Theaninova/Brick-Monorail/STEPs/solid/R28/S8.step

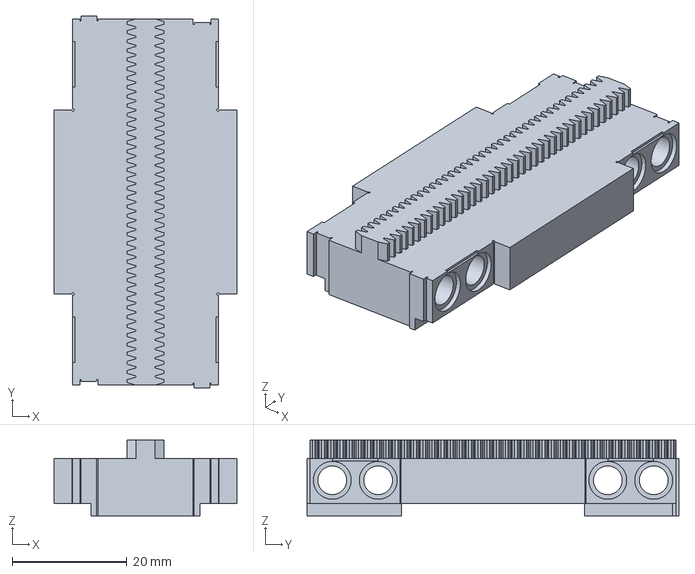
[picture p15: CAD file, 2025-01-19]
STEPs/solid/R28/S8.step
31.8 x 64.8 x 13.2 mm
