Theaninova/Brick-Monorail/STEPs/solid/S5.step

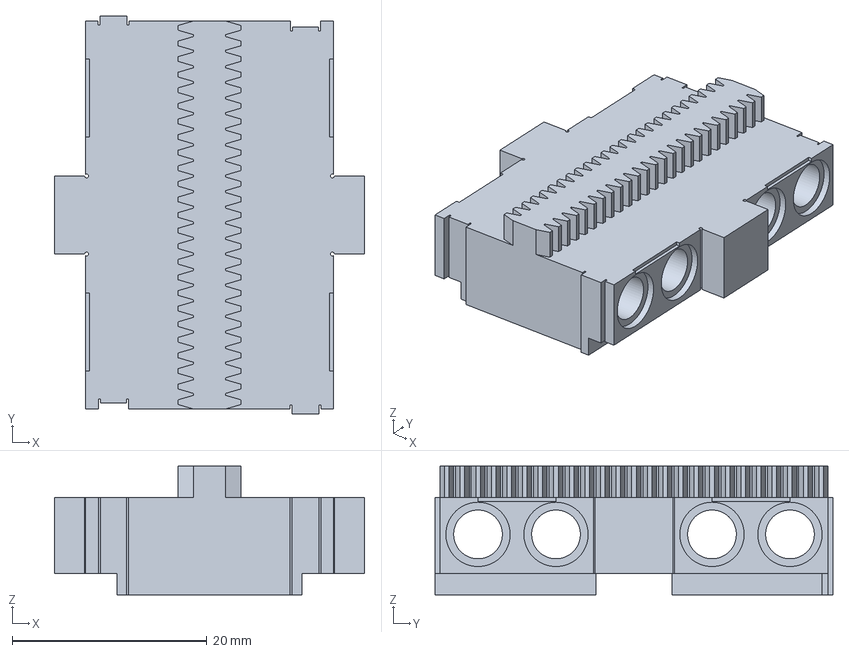
[picture p16: CAD file, 2025-01-19]
STEPs/solid/S5.step
31.8 x 40.8 x 13.2 mm
