Theaninova/Brick-Monorail/STEPs/solid_support/R28/C45_support.step

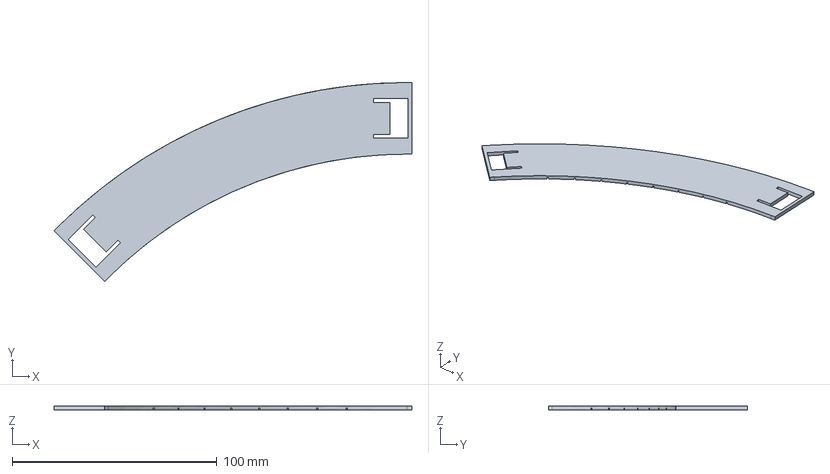
[picture p17: CAD file, 2025-01-19]
STEPs/solid_support/R28/C45_support.step
175.0 x 97.3 x 2.10 mm
