Theaninova/Brick-Monorail/STEPs/solid_support/S5.step

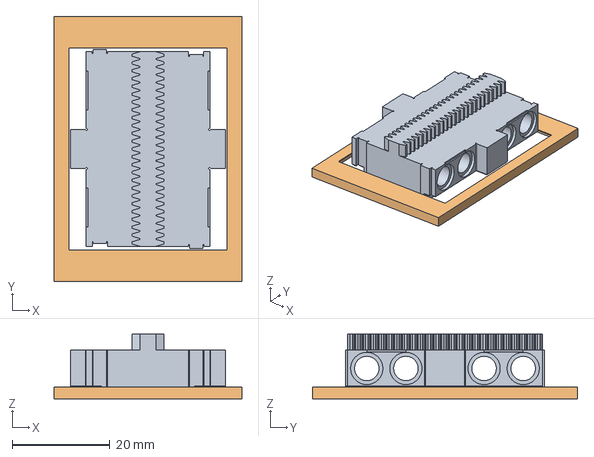
[picture p18: CAD file, 2025-01-19]
STEPs/solid_support/S5.step
38.4 x 54.2 x 13.2 mm
