Theaninova/Brick-Monorail/STEPs/stanchions/2x2x3.step

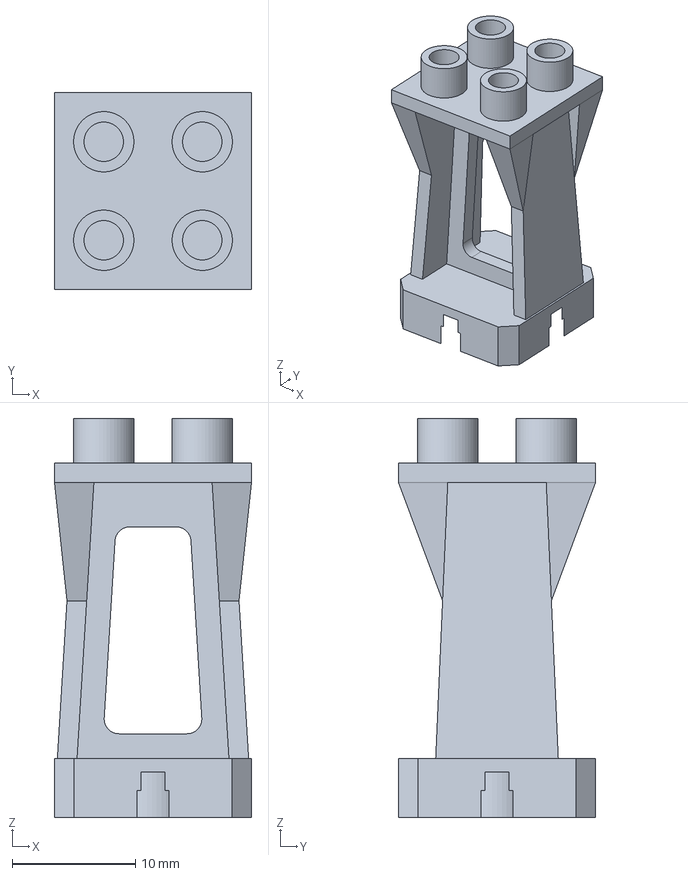
[picture p19: CAD file, 2025-01-19]
STEPs/stanchions/2x2x3.step
16.0 x 16.0 x 32.4 mm
