Theaninova/Brick-Monorail/STEPs/transrapid/S10.step

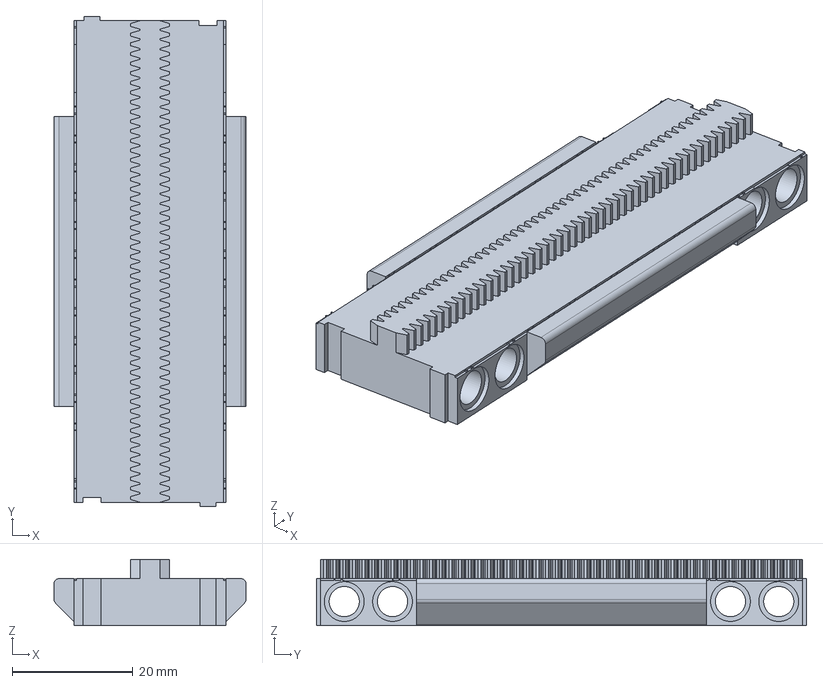
[picture p20: CAD file, 2025-01-19]
STEPs/transrapid/S10.step
31.8 x 81.2 x 11.0 mm
