Theaninova/Brick-Monorail/STEPs/classic/S4.step

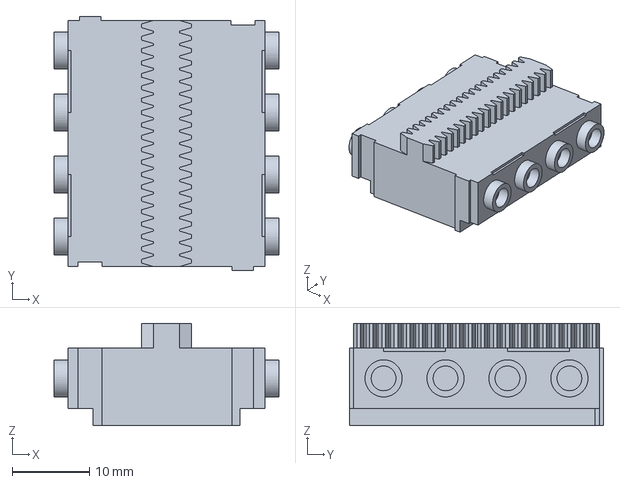
[picture p21: CAD file, 2025-01-19]
STEPs/classic/S4.step
29.0 x 32.8 x 13.2 mm
