Theaninova/Brick-Monorail/STEPs/classic_pop/R28/S8_body.step

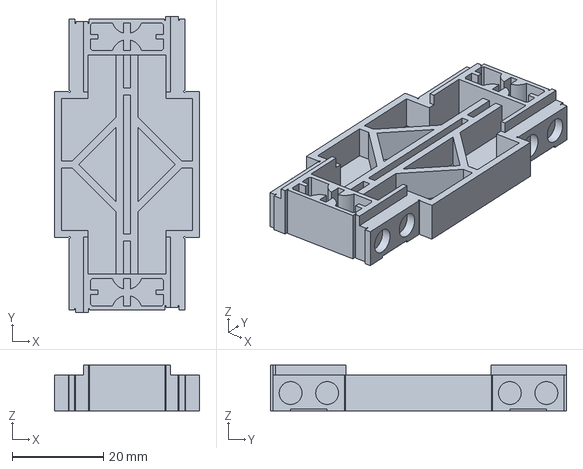
[picture p22: CAD file, 2025-01-19]
STEPs/classic_pop/R28/S8_body.step
31.8 x 64.8 x 10.0 mm
