Theaninova/Brick-Monorail/STEPs/classic_pop/S10_rack.step

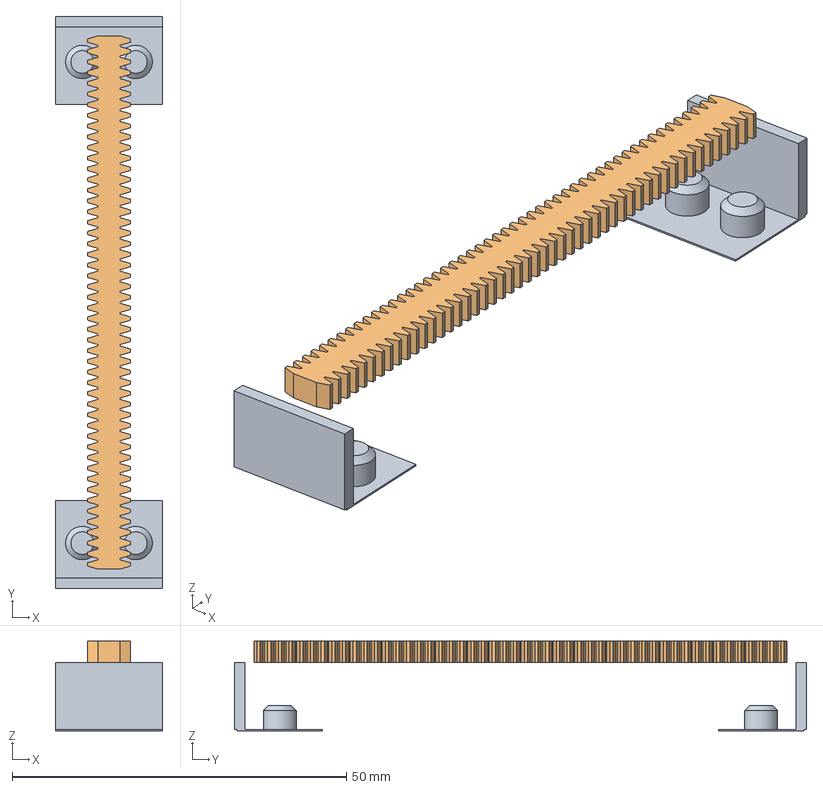
[picture p23: CAD file, 2025-01-19]
STEPs/classic_pop/S10_rack.step
16.0 x 85.6 x 13.4 mm
