Theaninova/Brick-Monorail/STEPs/solid/S15.step

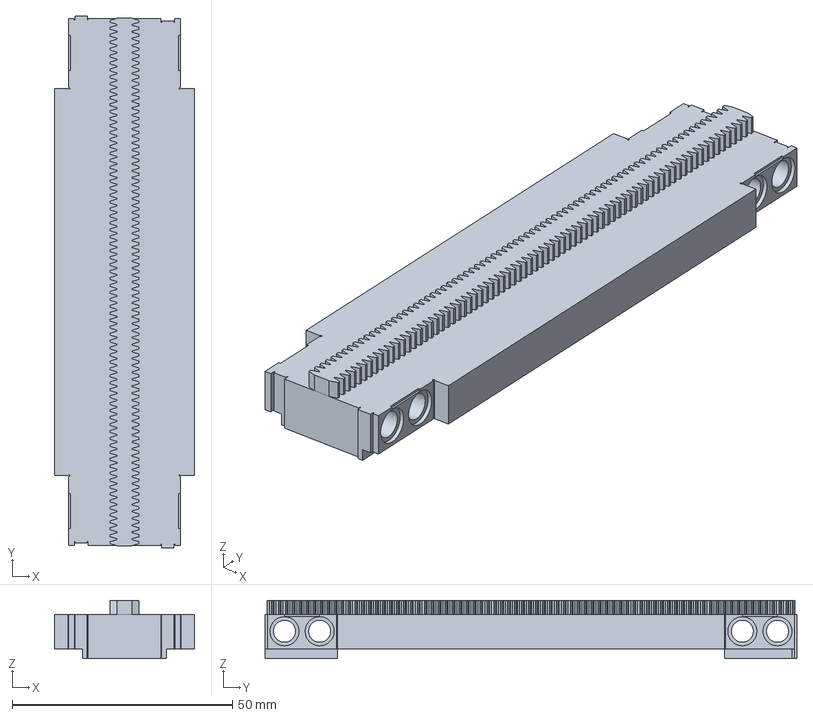
[picture p24: CAD file, 2025-01-19]
STEPs/solid/S15.step
31.8 x 120.8 x 13.2 mm
