Theaninova/Brick-Monorail/STEPs/solid_support/R28/S32_support.step

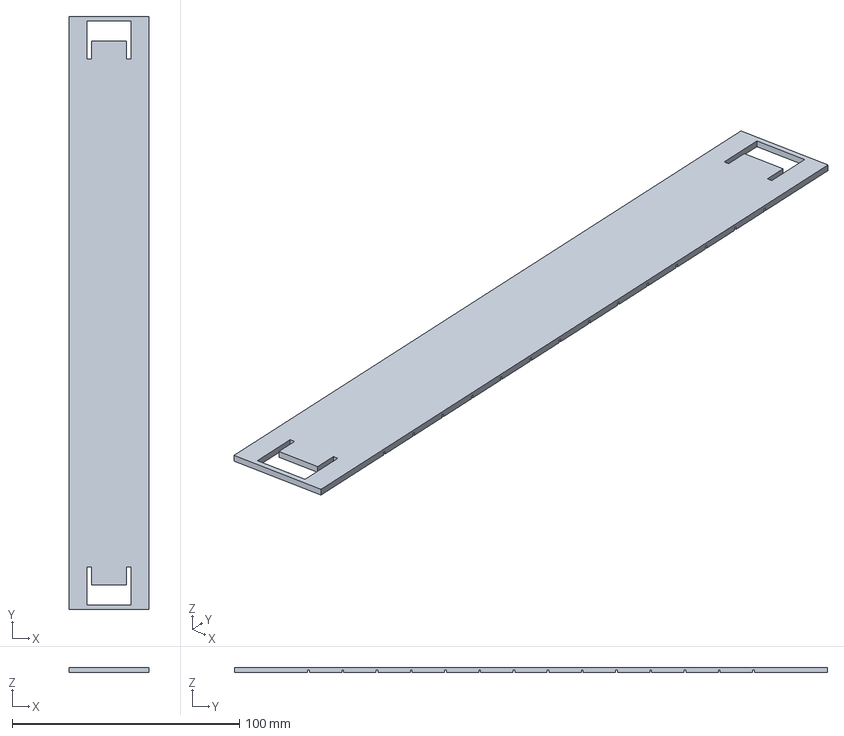
[picture p25: CAD file, 2025-01-19]
STEPs/solid_support/R28/S32_support.step
35.0 x 261.0 x 2.10 mm
