Theaninova/Brick-Monorail/STEPs/solid_support/S5_support.step

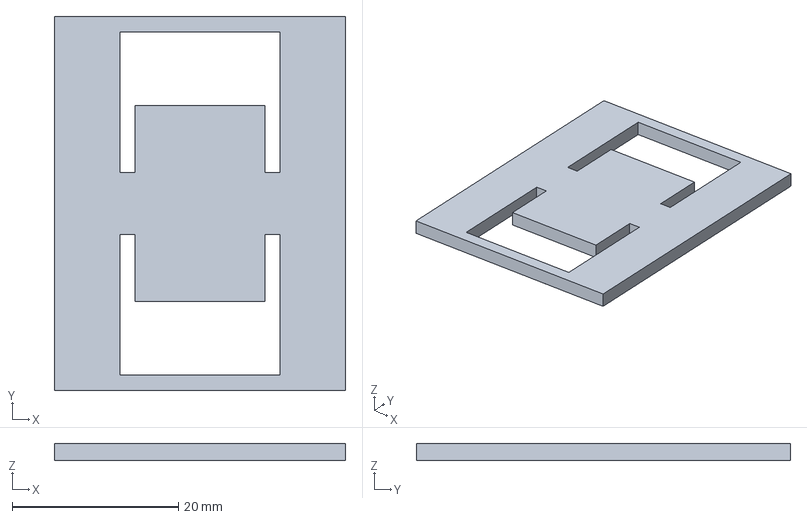
[picture p26: CAD file, 2025-01-19]
STEPs/solid_support/S5_support.step
35.0 x 45.0 x 2.10 mm
