Theaninova/Brick-Monorail/STEPs/stanchions/4x4x4.step

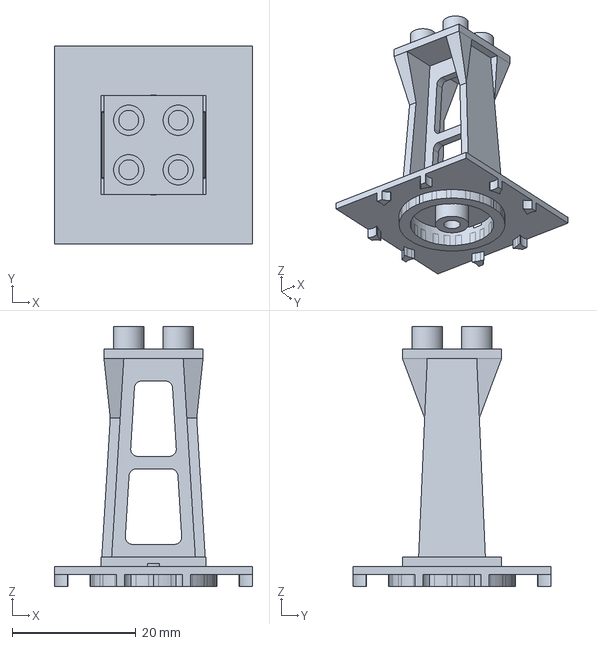
[picture p27: CAD file, 2025-01-19]
STEPs/stanchions/4x4x4.step
32.0 x 32.0 x 42.0 mm
