Theaninova/Brick-Monorail/STEPs/transrapid/C7.step

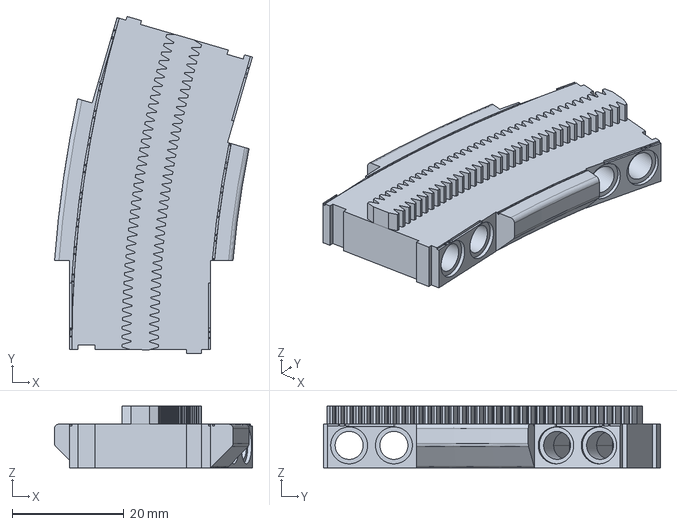
[picture p28: CAD file, 2025-01-19]
STEPs/transrapid/C7.step
35.4 x 60.2 x 11.0 mm
