Theaninova/Brick-Monorail/STEPs/classic/C7.step

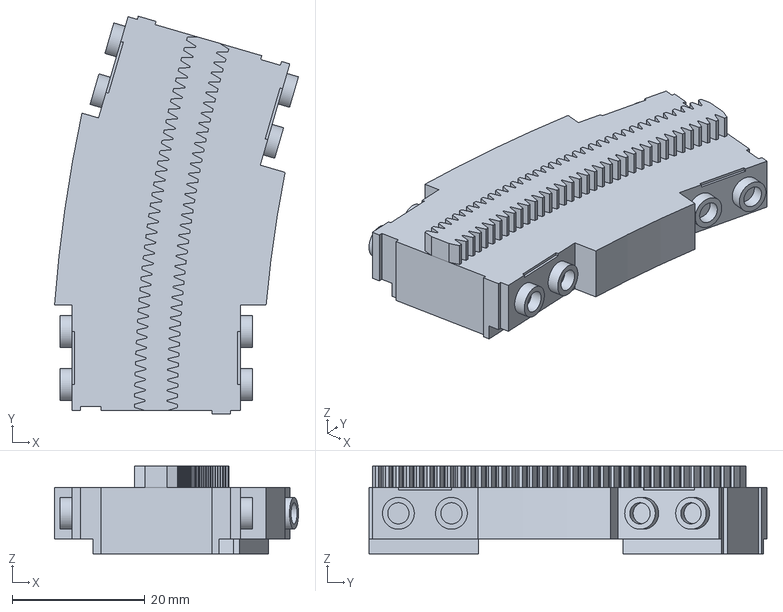
[picture p29: CAD file, 2025-01-19]
STEPs/classic/C7.step
36.8 x 59.9 x 13.2 mm
