Theaninova/Brick-Monorail/STEPs/classic_pop/R28/C45_body.step

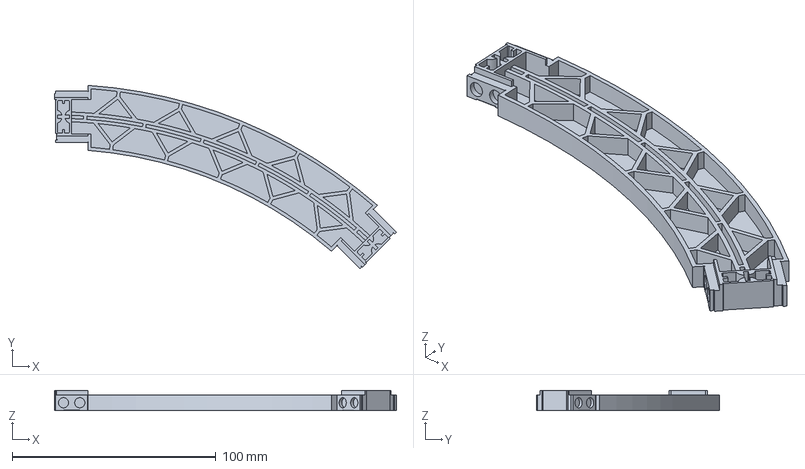
[picture p30: CAD file, 2025-01-19]
STEPs/classic_pop/R28/C45_body.step
167.7 x 89.9 x 10.0 mm
