Theaninova/Brick-Monorail/STEPs/classic_pop/S15_body.step

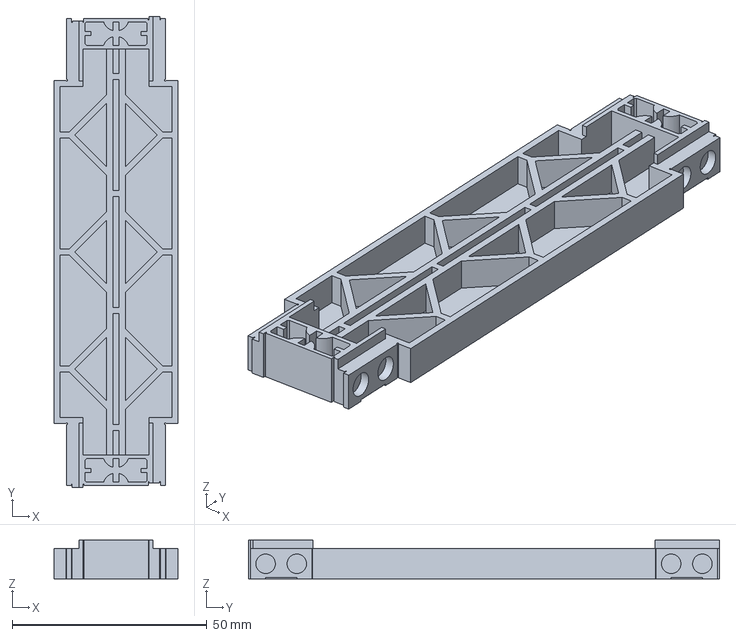
[picture p31: CAD file, 2025-01-19]
STEPs/classic_pop/S15_body.step
31.8 x 120.8 x 10.0 mm
