Theaninova/Brick-Monorail/STEPs/solid/C15.step

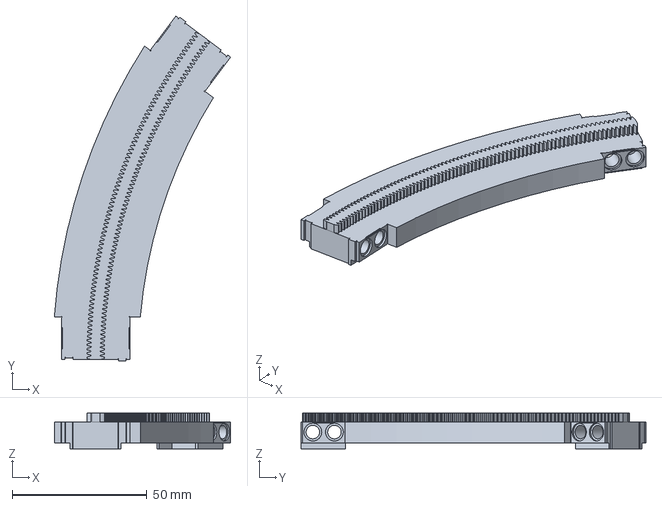
[picture p32: CAD file, 2025-01-19]
STEPs/solid/C15.step
65.4 x 127.9 x 13.2 mm
