Theaninova/Brick-Monorail/STEPs/solid_support/R28/C90_support.step

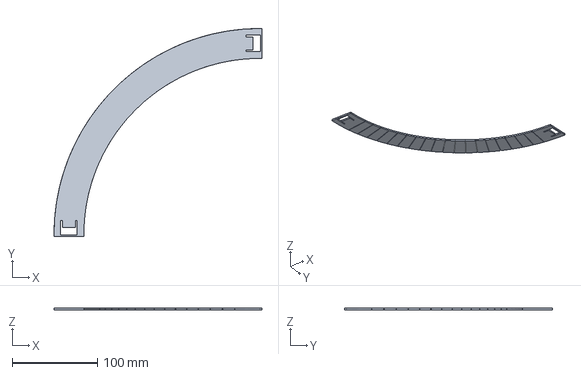
[picture p33: CAD file, 2025-01-19]
STEPs/solid_support/R28/C90_support.step
244.0 x 244.0 x 2.10 mm
