Theaninova/Brick-Monorail/STEPs/solid_support/S4.step

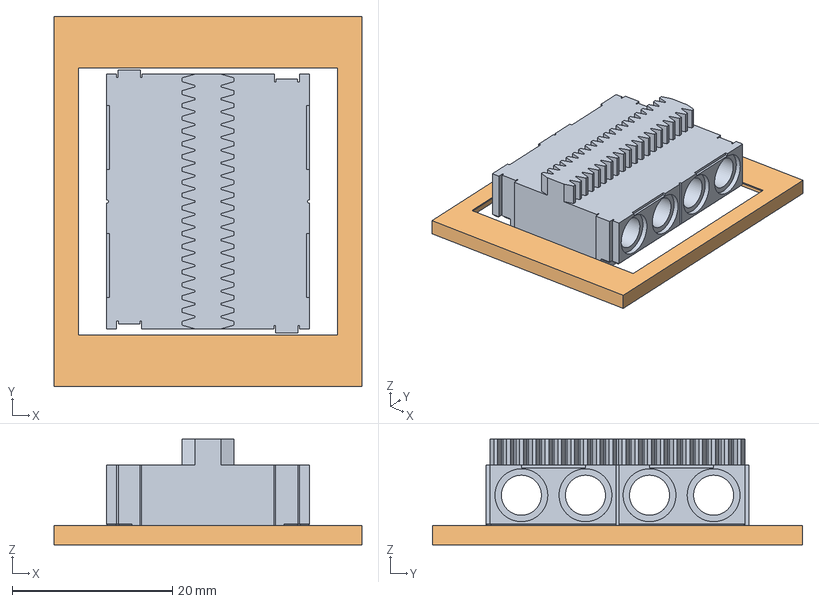
[picture p34: CAD file, 2025-01-19]
STEPs/solid_support/S4.step
38.4 x 46.2 x 13.2 mm
