Theaninova/Brick-Monorail/STEPs/stanchions/4x4x5.step

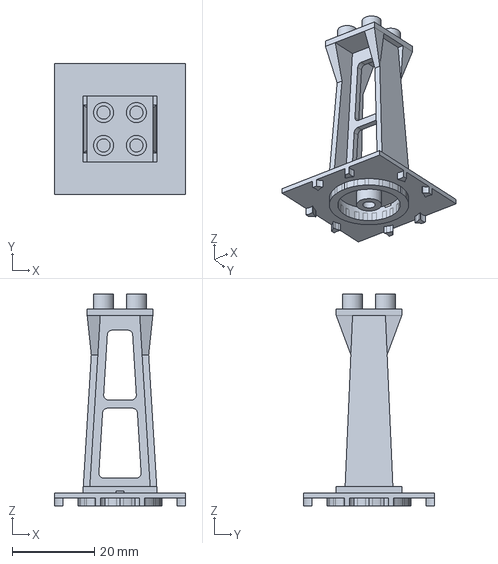
[picture p35: CAD file, 2025-01-19]
STEPs/stanchions/4x4x5.step
32.0 x 32.0 x 51.6 mm
