Theaninova/Brick-Monorail/STEPs/transrapid/S5.step

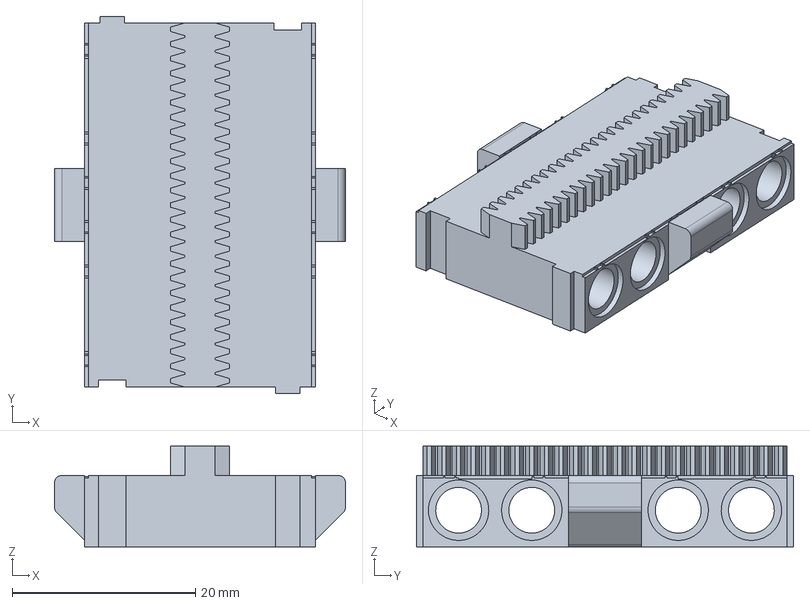
[picture p36: CAD file, 2025-01-19]
STEPs/transrapid/S5.step
31.8 x 41.2 x 11.0 mm
