Theaninova/Brick-Monorail/STEPs/classic/S10.step

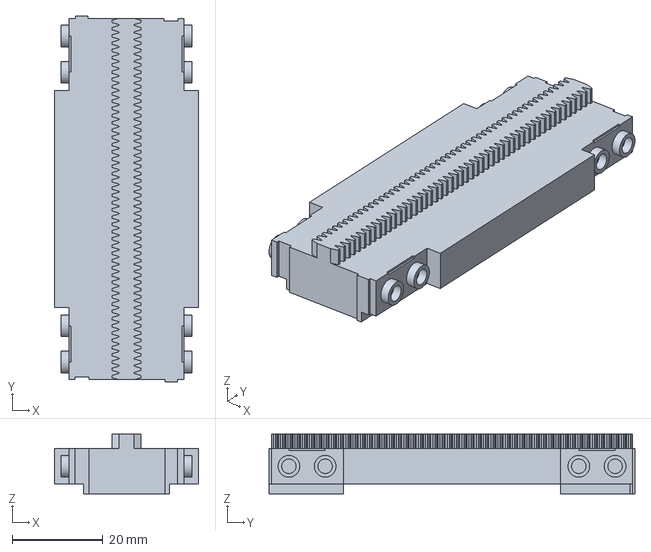
[picture p37: CAD file, 2025-01-19]
STEPs/classic/S10.step
31.8 x 80.8 x 13.2 mm
