Theaninova/Brick-Monorail/STEPs/classic_pop/R28/S8_rack.step

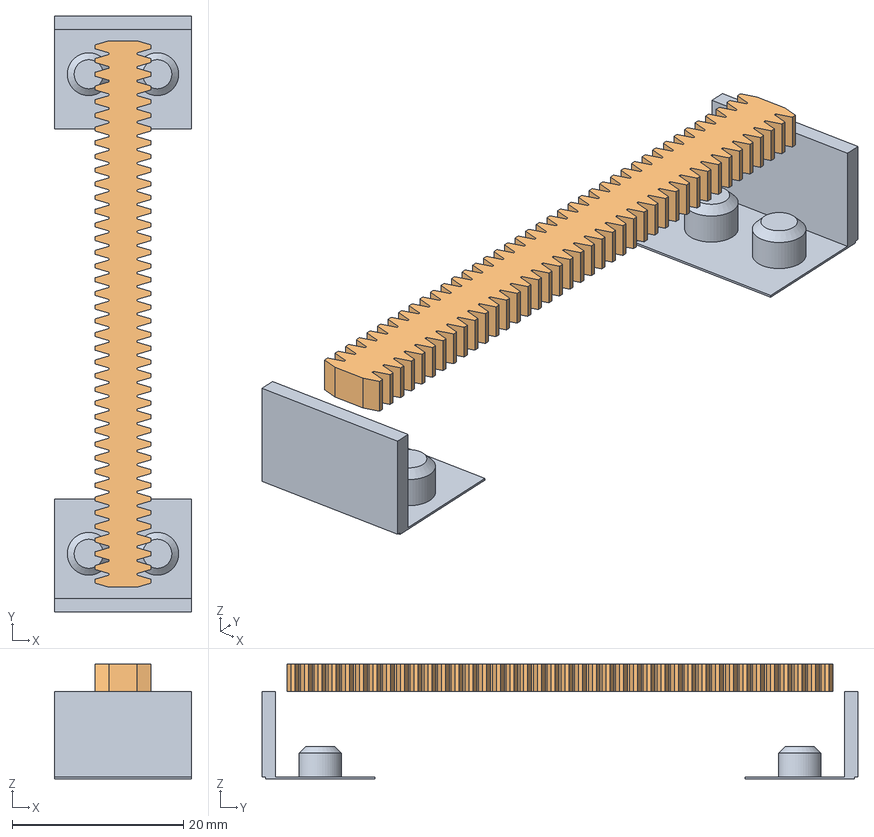
[picture p38: CAD file, 2025-01-19]
STEPs/classic_pop/R28/S8_rack.step
16.0 x 69.6 x 13.4 mm
