Theaninova/Brick-Monorail/STEPs/classic_pop/S25_body.step

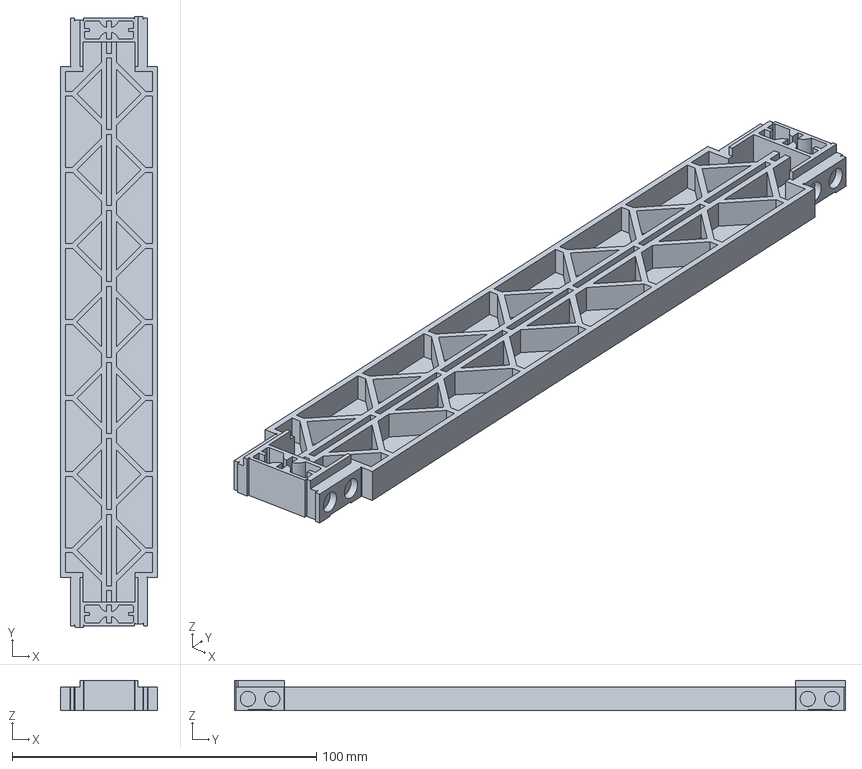
[picture p39: CAD file, 2025-01-19]
STEPs/classic_pop/S25_body.step
31.8 x 200.8 x 10.0 mm
