Theaninova/Brick-Monorail/STEPs/solid/S10.step

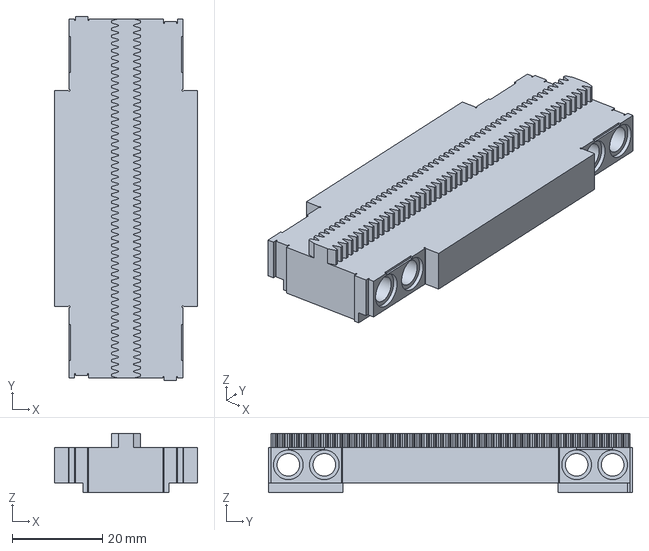
[picture p40: CAD file, 2025-01-19]
STEPs/solid/S10.step
31.8 x 80.8 x 13.2 mm
