Theaninova/Brick-Monorail/STEPs/solid_support/R28/S16_support.step

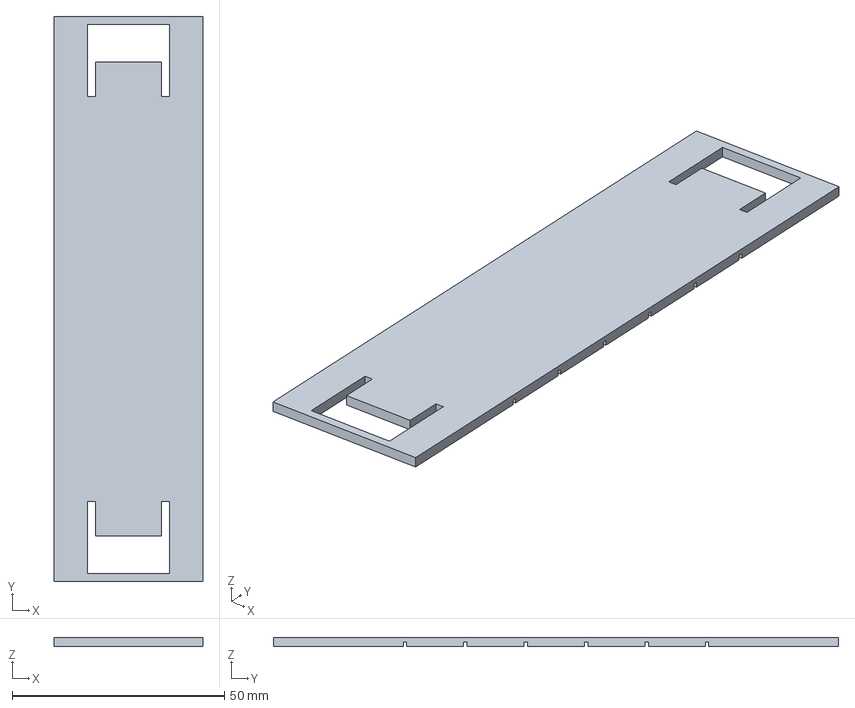
[picture p41: CAD file, 2025-01-19]
STEPs/solid_support/R28/S16_support.step
35.0 x 133.0 x 2.10 mm
