Theaninova/Brick-Monorail/STEPs/solid_support/S10_support.step

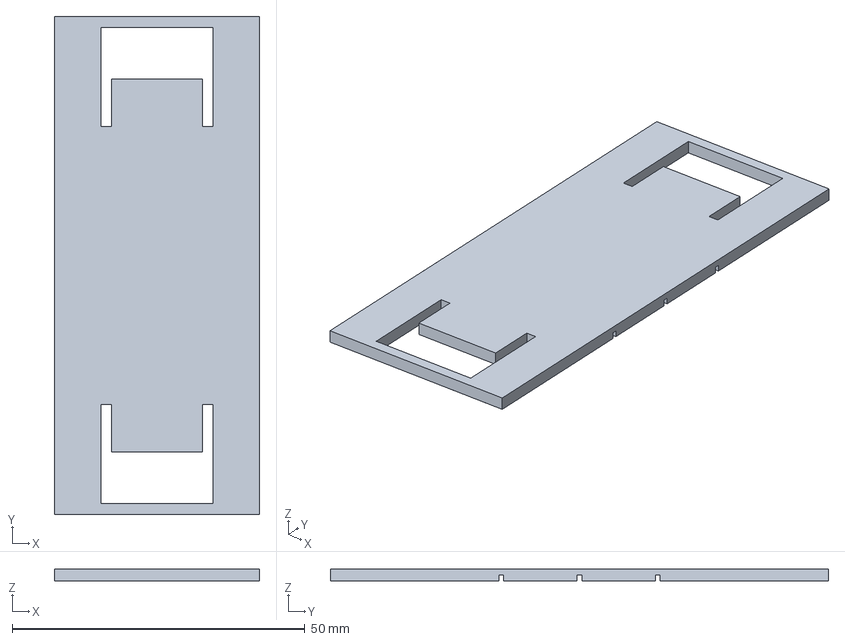
[picture p42: CAD file, 2025-01-19]
STEPs/solid_support/S10_support.step
35.0 x 85.0 x 2.10 mm
