Theaninova/Brick-Monorail/STEPs/stanchions/4x4x3.step

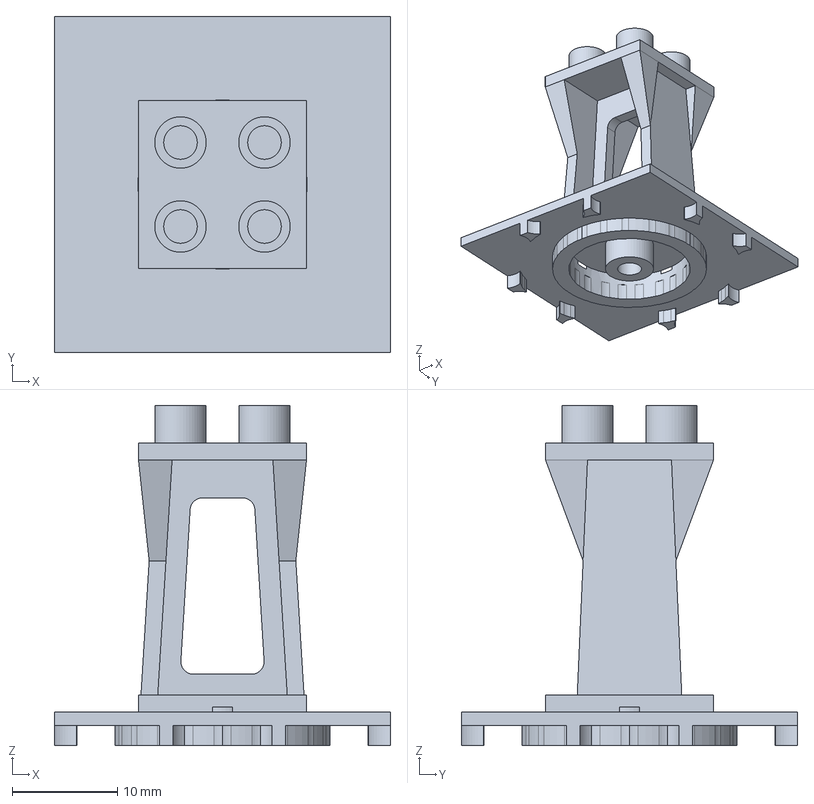
[picture p43: CAD file, 2025-01-19]
STEPs/stanchions/4x4x3.step
32.0 x 32.0 x 32.4 mm
