Theaninova/Brick-Monorail/STEPs/classic_pop/R28/C90_body.step

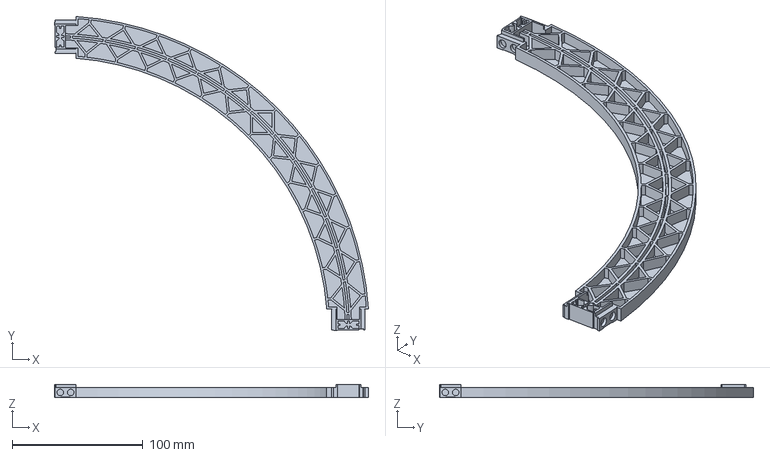
[picture p44: CAD file, 2025-01-19]
STEPs/classic_pop/R28/C90_body.step
239.8 x 239.8 x 10.0 mm
