Theaninova/Brick-Monorail/STEPs/classic_pop/S5_rack.step

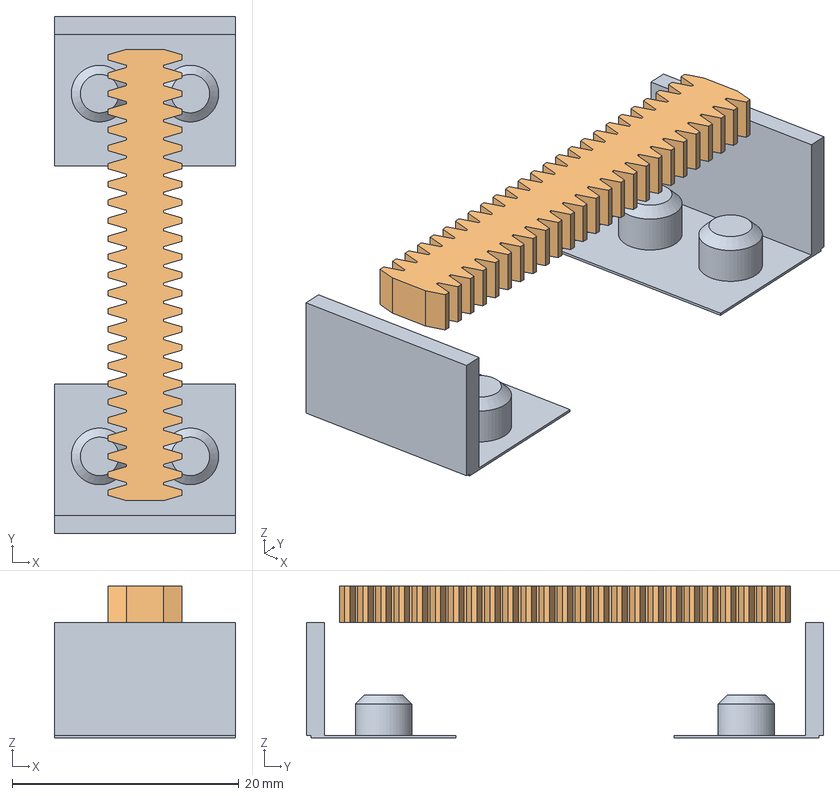
[picture p45: CAD file, 2025-01-19]
STEPs/classic_pop/S5_rack.step
16.0 x 45.6 x 13.4 mm
