Theaninova/Brick-Monorail/STEPs/solid/C7.step

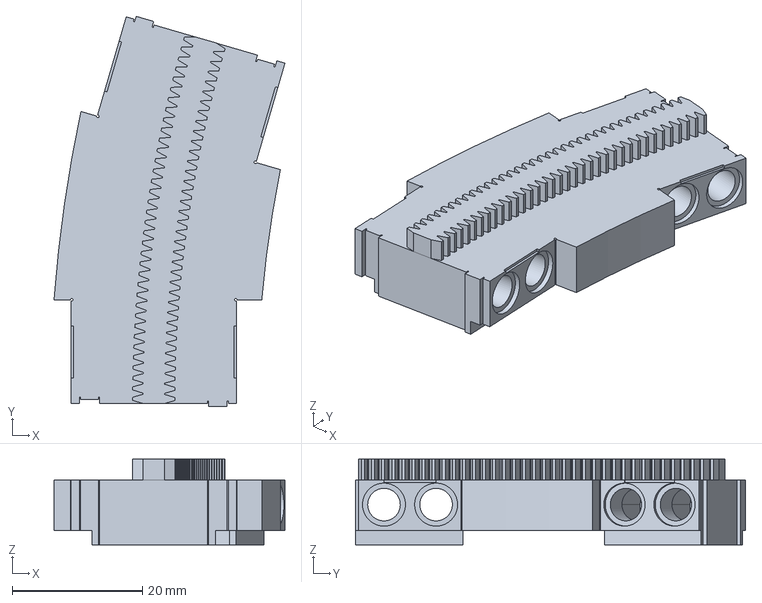
[picture p46: CAD file, 2025-01-19]
STEPs/solid/C7.step
35.5 x 59.9 x 13.2 mm
