Theaninova/Brick-Monorail/STEPs/solid_support/R28/S8_support.step

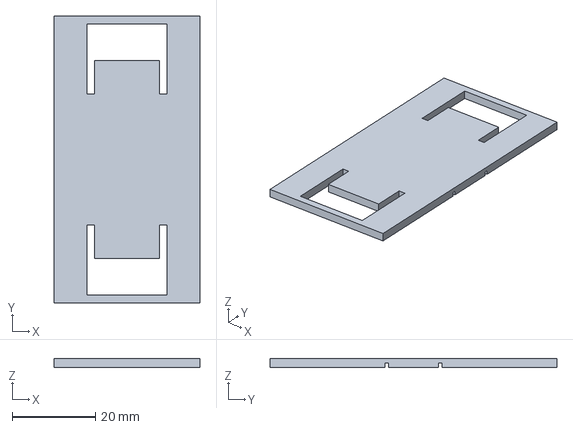
[picture p47: CAD file, 2025-01-19]
STEPs/solid_support/R28/S8_support.step
35.0 x 69.0 x 2.10 mm
