Theaninova/Brick-Monorail/STEPs/solid_support/S10.step

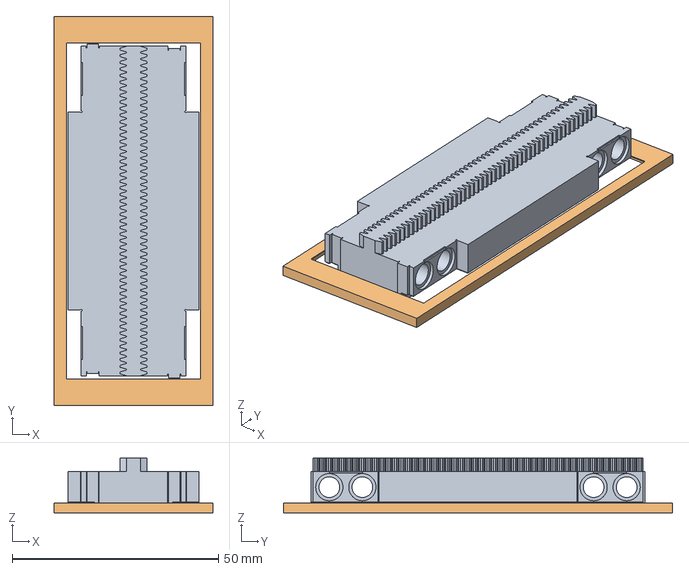
[picture p48: CAD file, 2025-01-19]
STEPs/solid_support/S10.step
38.4 x 94.2 x 13.2 mm
