Theaninova/Brick-Monorail/STEPs/stanchions/2x2x1.step

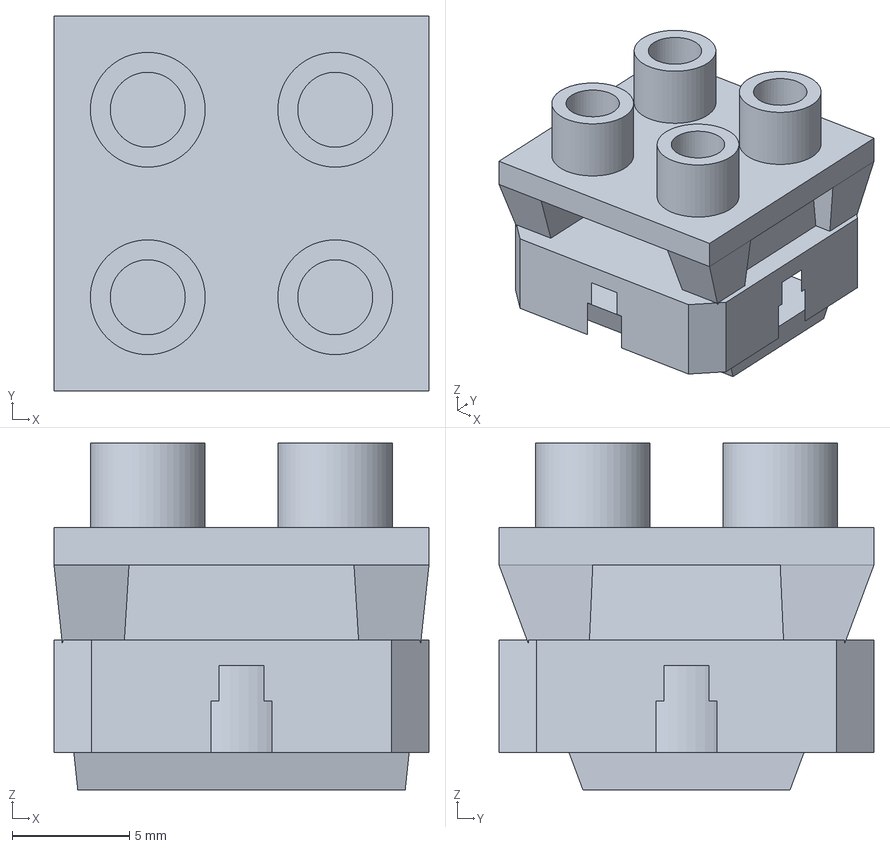
[picture p49: CAD file, 2025-01-19]
STEPs/stanchions/2x2x1.step
16.0 x 16.0 x 14.8 mm
