Theaninova/Brick-Monorail/STEPs/classic_pop/C15_body.step

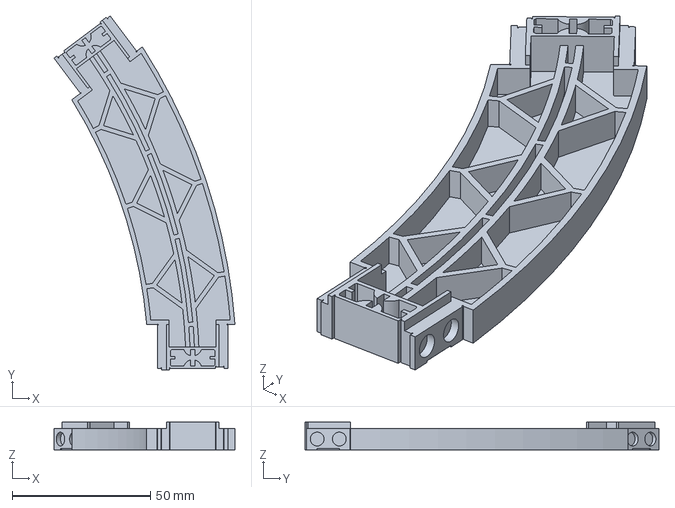
[picture p50: CAD file, 2025-01-19]
STEPs/classic_pop/C15_body.step
65.4 x 127.9 x 10.0 mm
