Theaninova/Brick-Monorail/STEPs/classic_pop/R28/S32_body.step

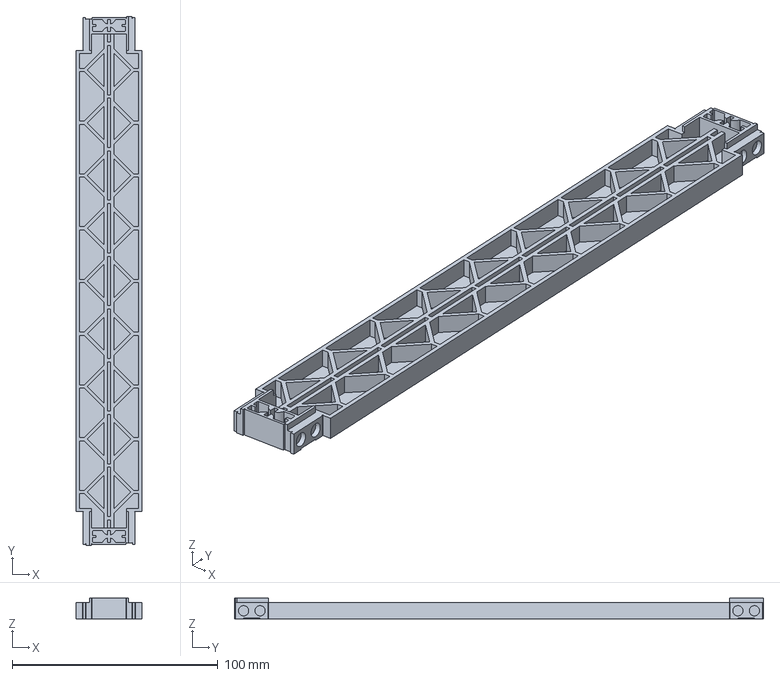
[picture p51: CAD file, 2025-01-19]
STEPs/classic_pop/R28/S32_body.step
31.8 x 256.8 x 10.0 mm
