Theaninova/Brick-Monorail/STEPs/solid_support/R28/S16.step

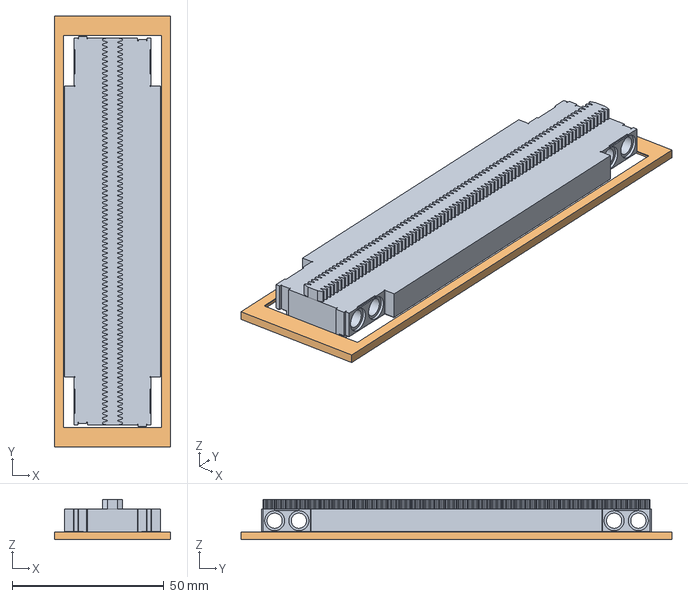
[picture p52: CAD file, 2025-01-19]
STEPs/solid_support/R28/S16.step
38.4 x 142.2 x 13.2 mm
