Theaninova/Brick-Monorail/STEPs/solid_support/S15.step

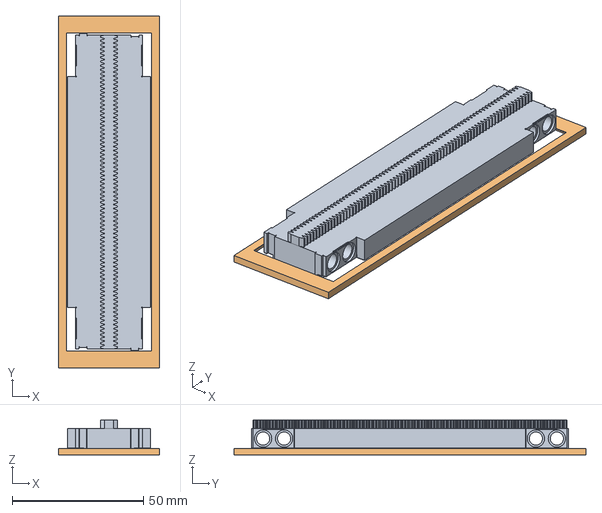
[picture p53: CAD file, 2025-01-19]
STEPs/solid_support/S15.step
38.4 x 134.2 x 13.2 mm
