Theaninova/Brick-Monorail/STEPs/stanchions/6x6x10.step

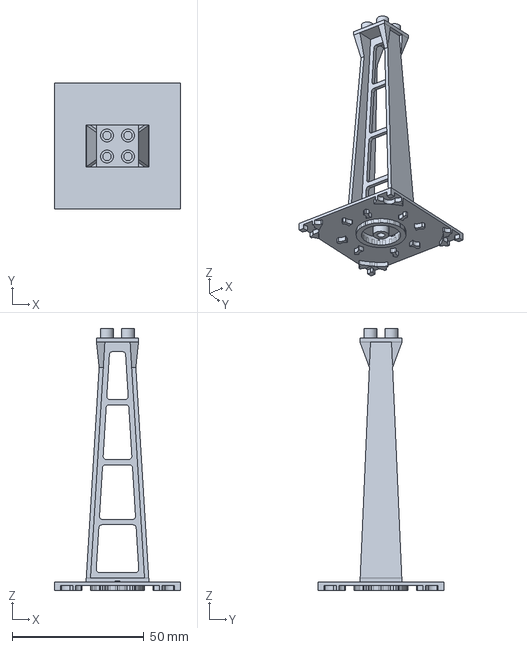
[picture p54: CAD file, 2025-01-19]
STEPs/stanchions/6x6x10.step
48.0 x 48.0 x 99.6 mm
