Theaninova/Brick-Monorail/STEPs/classic_pop/S10_body.step

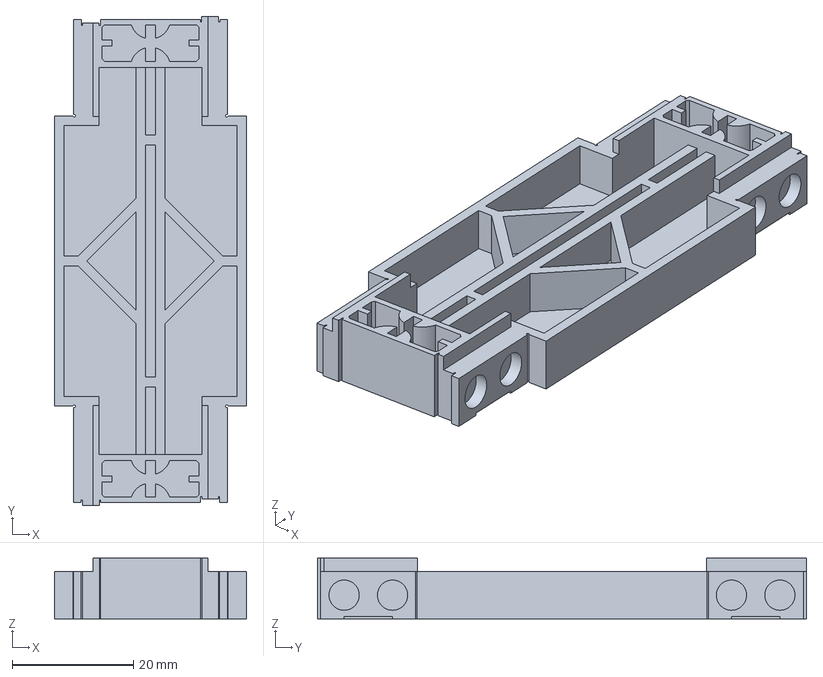
[picture p55: CAD file, 2025-01-19]
STEPs/classic_pop/S10_body.step
31.8 x 80.8 x 10.0 mm
