Theaninova/Brick-Monorail/STEPs/solid_support/C7.step

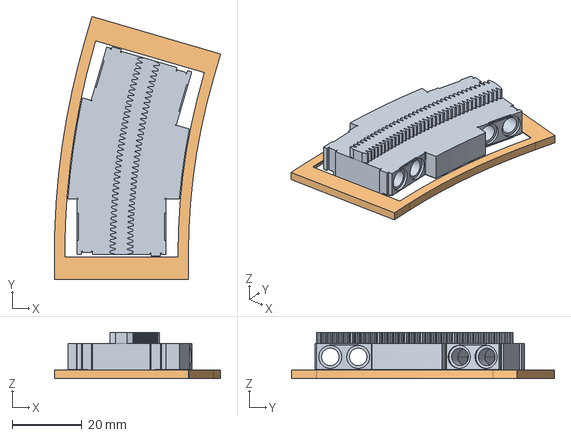
[picture p56: CAD file, 2025-01-19]
STEPs/solid_support/C7.step
47.6 x 75.3 x 13.2 mm
