Theaninova/Brick-Monorail/STEPs/stanchions/2x2x2.step

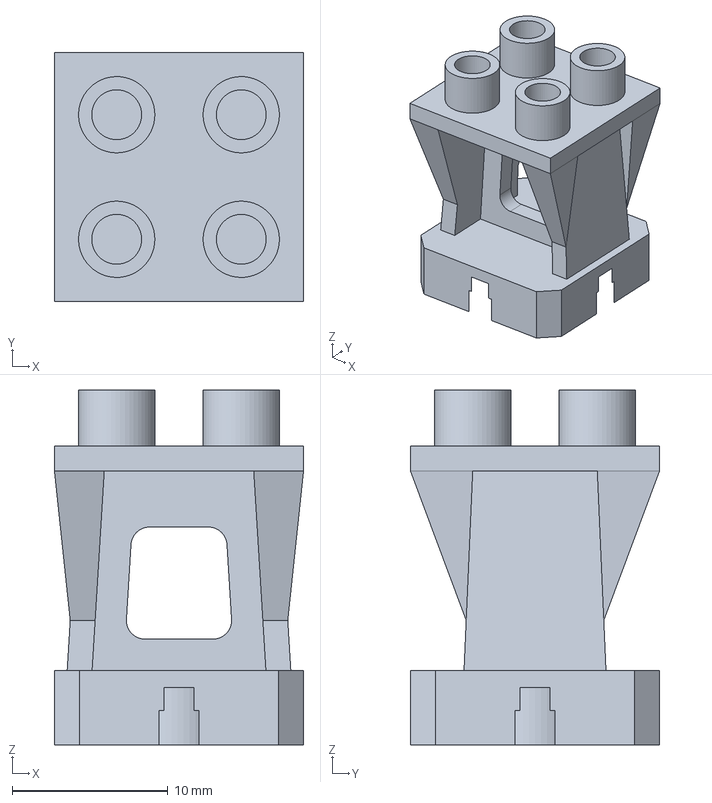
[picture p57: CAD file, 2025-01-19]
STEPs/stanchions/2x2x2.step
16.0 x 16.0 x 22.8 mm
