Theaninova/Brick-Monorail/STEPs/classic_pop/S25_rack.step

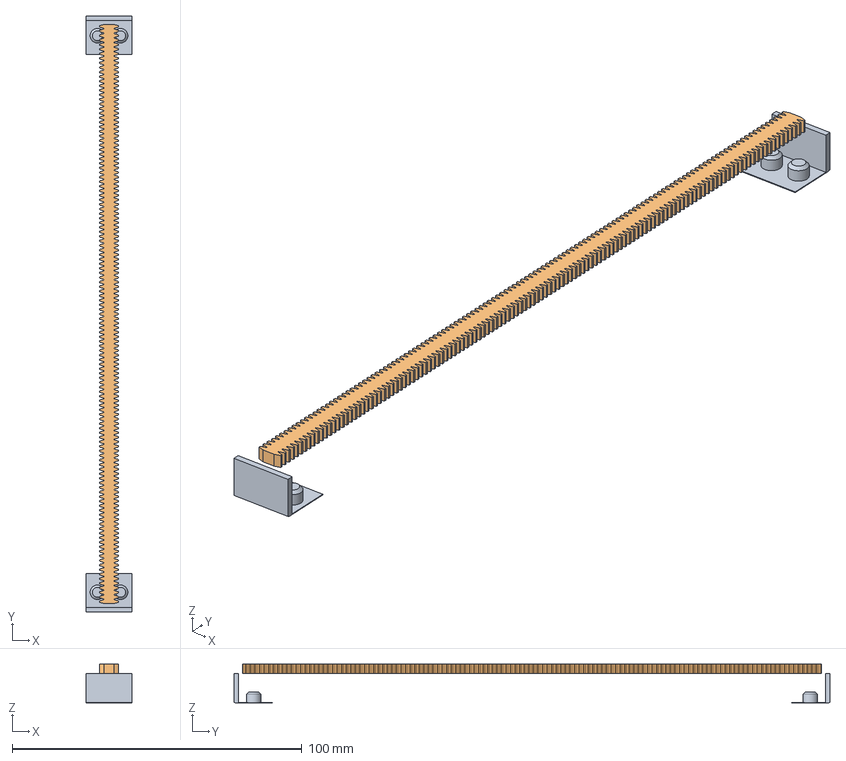
[picture p58: CAD file, 2025-01-19]
STEPs/classic_pop/S25_rack.step
16.0 x 205.6 x 13.4 mm
