Theaninova/Brick-Monorail/STEPs/solid_support/S25_support.step

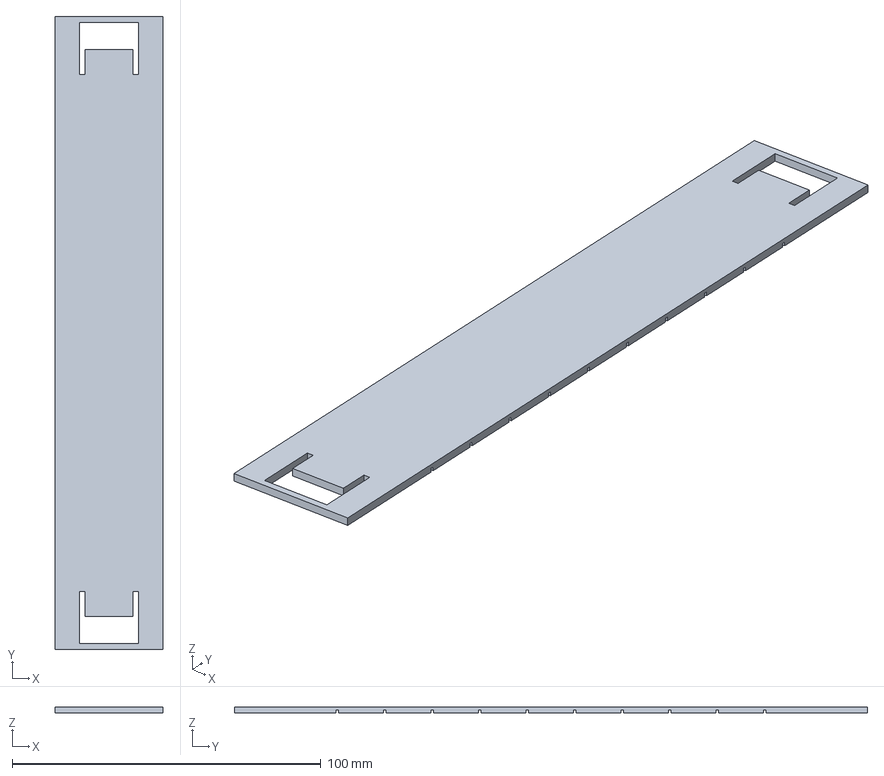
[picture p59: CAD file, 2025-01-19]
STEPs/solid_support/S25_support.step
35.0 x 205.0 x 2.10 mm
