Theaninova/Brick-Monorail/STEPs/stanchions/2x2x4.step

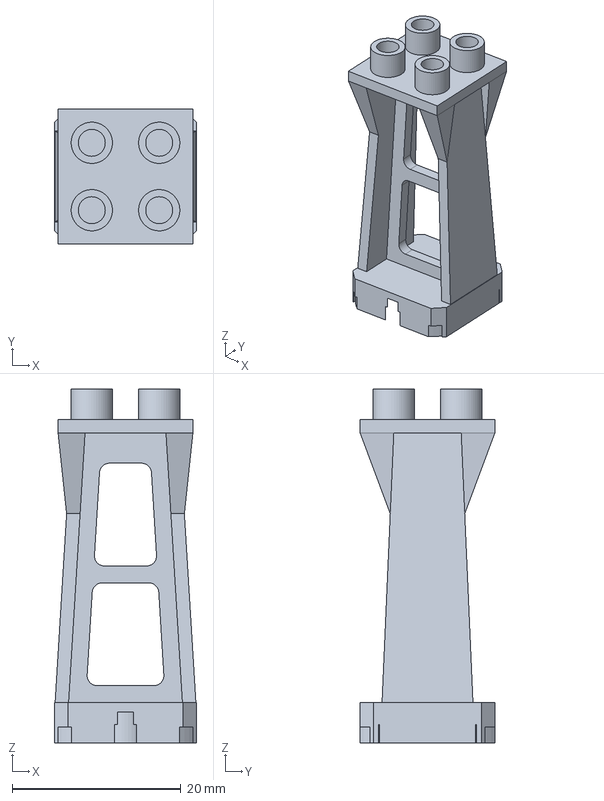
[picture p60: CAD file, 2025-01-19]
STEPs/stanchions/2x2x4.step
16.9 x 16.0 x 42.0 mm
