Theaninova/Brick-Monorail/STEPs/classic_pop/C7_rack.step

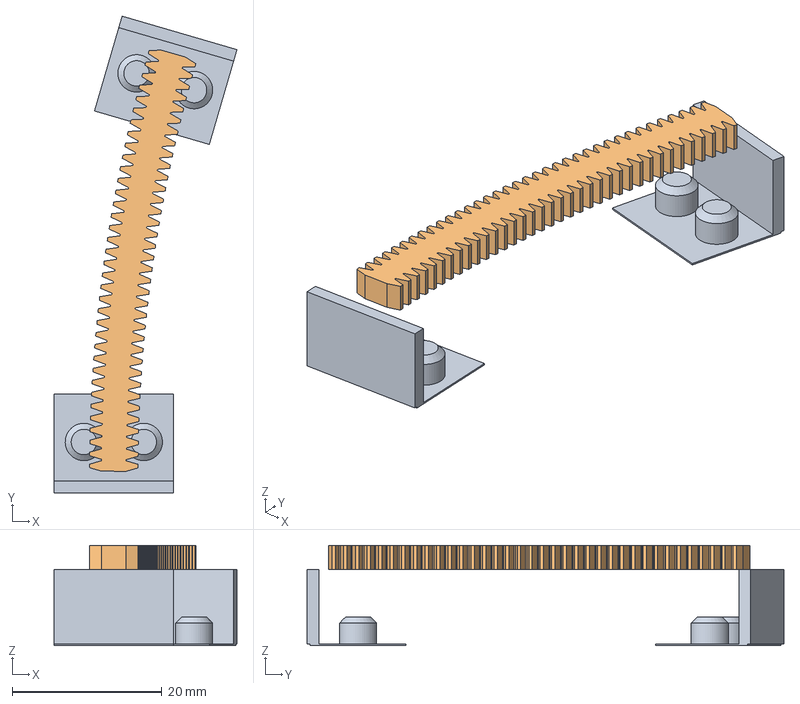
[picture p61: CAD file, 2025-01-19]
STEPs/classic_pop/C7_rack.step
24.5 x 63.7 x 13.4 mm
