Theaninova/Brick-Monorail/STEPs/solid_support/S4_support.step

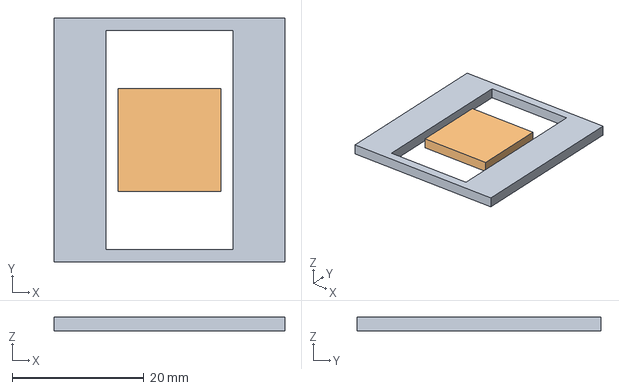
[picture p62: CAD file, 2025-01-19]
STEPs/solid_support/S4_support.step
35.0 x 37.0 x 2.10 mm
