Theaninova/Brick-Monorail/STEPs/classic_pop/S5_body.step

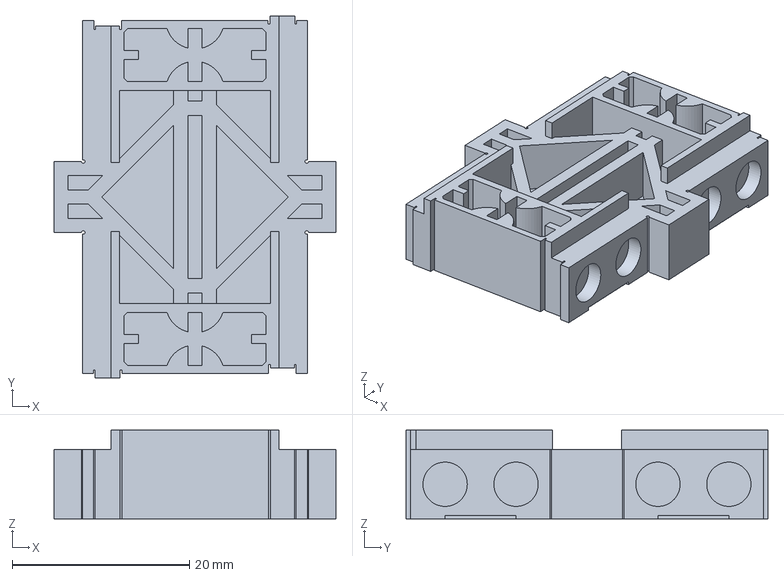
[picture p63: CAD file, 2025-01-19]
STEPs/classic_pop/S5_body.step
31.8 x 40.8 x 10.0 mm
