Theaninova/Brick-Monorail/STEPs/solid_support/S15_support.step

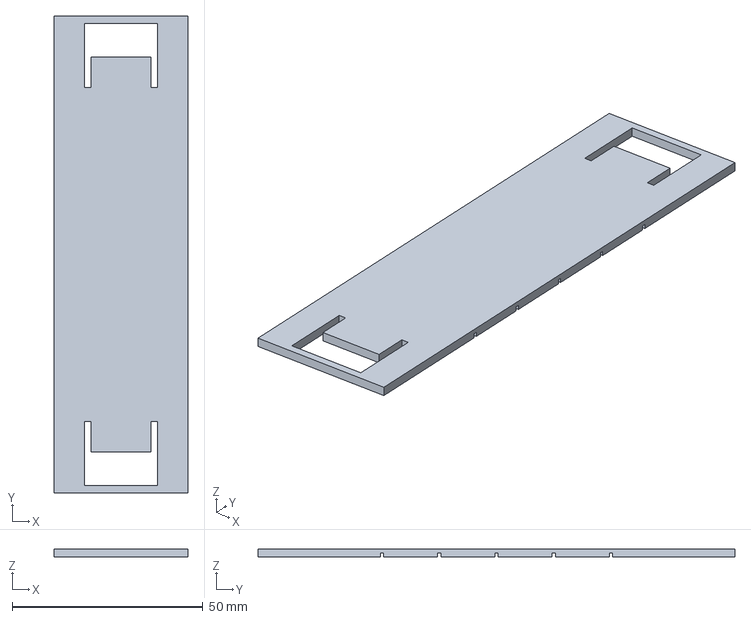
[picture p64: CAD file, 2025-01-19]
STEPs/solid_support/S15_support.step
35.0 x 125.0 x 2.10 mm
