Theaninova/Brick-Monorail/STEPs/classic_pop/S4_body.step

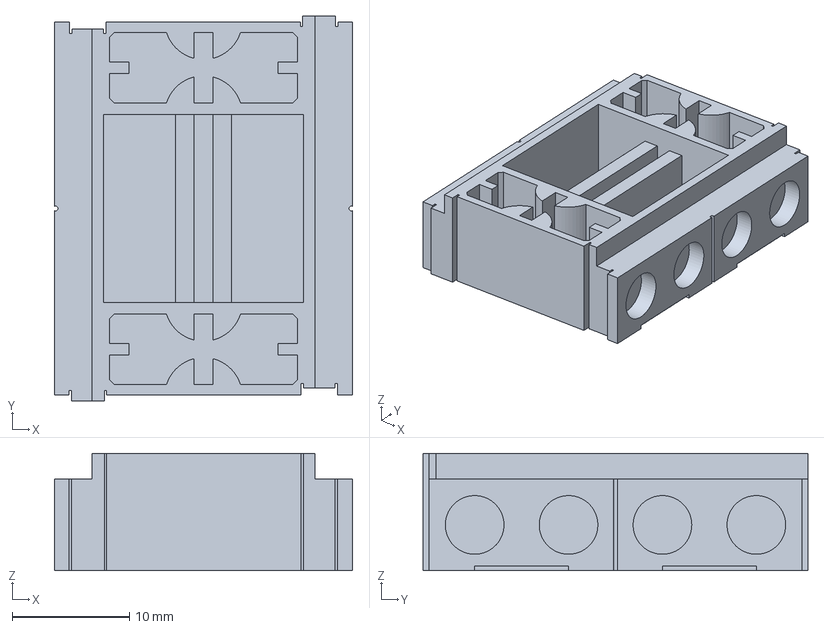
[picture p65: CAD file, 2025-01-19]
STEPs/classic_pop/S4_body.step
25.4 x 32.8 x 10.0 mm
