Theaninova/Brick-Monorail/STEPs/solid_support/C7_support.step

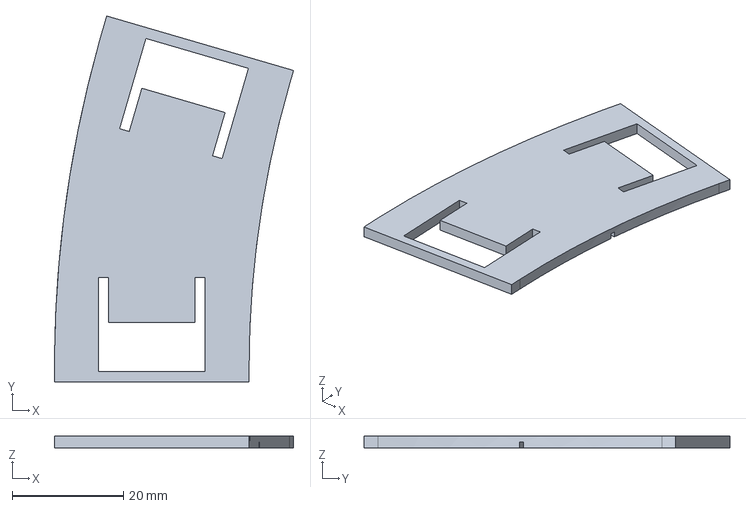
[picture p66: CAD file, 2025-01-19]
STEPs/solid_support/C7_support.step
43.0 x 65.8 x 2.10 mm
