Theaninova/Brick-Monorail/STEPs/classic_pop/S4_rack.step

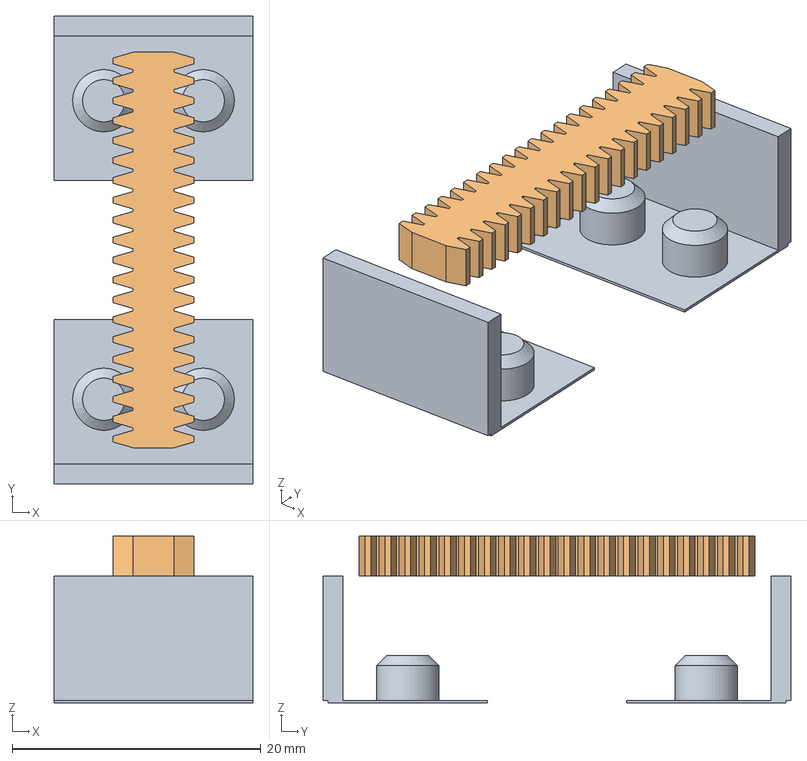
[picture p67: CAD file, 2025-01-19]
STEPs/classic_pop/S4_rack.step
16.0 x 37.6 x 13.4 mm
