Theaninova/Brick-Monorail/STEPs/solid_support/C15.step

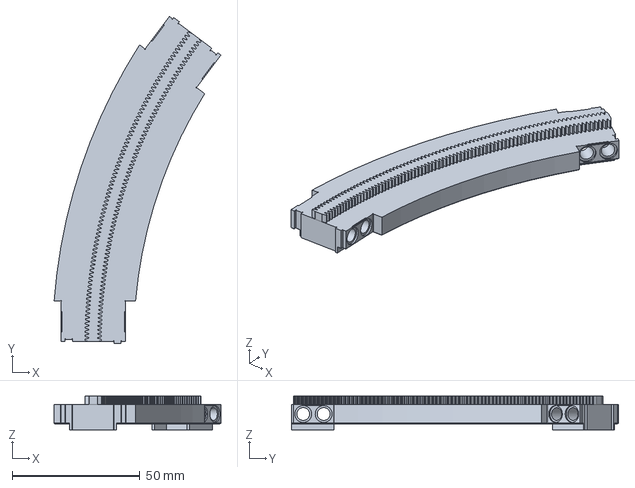
[picture p68: CAD file, 2024-11-25]
STEPs/solid_support/C15.step
65.3 x 128.1 x 13.2 mm
