Theaninova/Brick-Monorail/STEPs/classic_pop/C15_rack.step

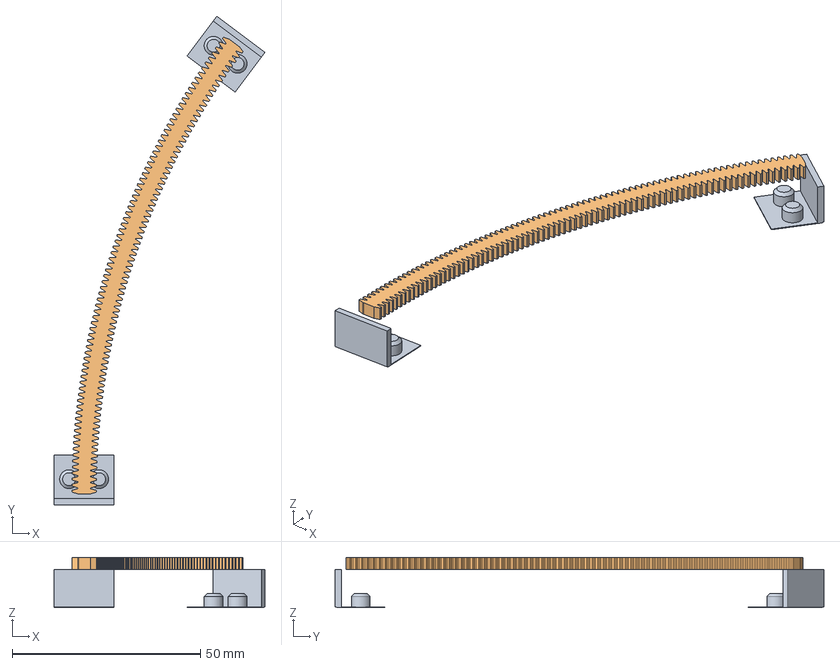
[picture p69: CAD file, 2025-01-19]
STEPs/classic_pop/C15_rack.step
56.1 x 129.8 x 13.4 mm
